arkadiraf/Trixel-LED/Bootloader/SparkFun ISP Pogo Adapter - KIT-11591 - SparkFun Electronics_files/09173-02-L.jpg

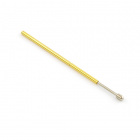
Bootloader/SparkFun ISP Pogo Adapter - KIT-11591 - SparkFun Electronics_files/09173-02-L.jpg
