arkadiraf/Trixel-LED/Bootloader/SparkFun ISP Pogo Adapter - KIT-11591 - SparkFun Electronics_files/09174-02-L.jpg

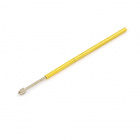
Bootloader/SparkFun ISP Pogo Adapter - KIT-11591 - SparkFun Electronics_files/09174-02-L.jpg
