arkadiraf/Trixel-LED/Bootloader/SparkFun ISP Pogo Adapter - KIT-11591 - SparkFun Electronics_files/09215-3.jpg

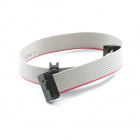
Bootloader/SparkFun ISP Pogo Adapter - KIT-11591 - SparkFun Electronics_files/09215-3.jpg
