arkadiraf/Trixel-LED/Bootloader/SparkFun ISP Pogo Adapter - KIT-11591 - SparkFun Electronics_files/10914-01.jpg

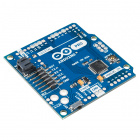
Bootloader/SparkFun ISP Pogo Adapter - KIT-11591 - SparkFun Electronics_files/10914-01.jpg
