arkadiraf/Trixel-LED/Bootloader/SparkFun ISP Pogo Adapter - KIT-11591 - SparkFun Electronics_files/14747-SparkFun_Pi_AVR_Programmer_HAT_-07.jpg

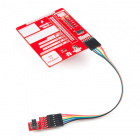
Bootloader/SparkFun ISP Pogo Adapter - KIT-11591 - SparkFun Electronics_files/14747-SparkFun_Pi_AVR_Programmer_HAT_-07.jpg
