arkadiraf/Trixel-LED/Bootloader/USBASP V2.0 Programmer for Atmel Microcontrollers - Art of Circuits_files/60x-9595-microscope-1-150x150.png

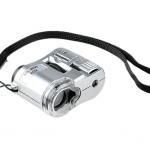
Bootloader/USBASP V2.0 Programmer for Atmel Microcontrollers - Art of Circuits_files/60x-9595-microscope-1-150x150.png
