arkadiraf/Trixel-LED/Bootloader/USBASP V2.0 Programmer for Atmel Microcontrollers - Art of Circuits_files/AVR-ISP-Adapter-10p-6p-1-150x150.jpg

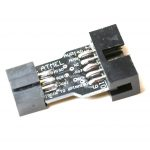
Bootloader/USBASP V2.0 Programmer for Atmel Microcontrollers - Art of Circuits_files/AVR-ISP-Adapter-10p-6p-1-150x150.jpg
