arkadiraf/Trixel-LED/Bootloader/USBASP V2.0 Programmer for Atmel Microcontrollers - Art of Circuits_files/DP30V5A-L_Digital_Power_Supply-1-150x150.jpg

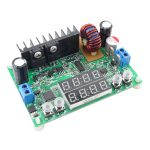
Bootloader/USBASP V2.0 Programmer for Atmel Microcontrollers - Art of Circuits_files/DP30V5A-L_Digital_Power_Supply-1-150x150.jpg
