arkadiraf/Trixel-LED/Bootloader/USBASP V2.0 Programmer for Atmel Microcontrollers - Art of Circuits_files/ELM327-OBD-Bluetooth-Tool-1-150x150.jpg

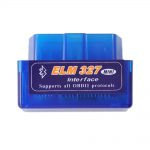
Bootloader/USBASP V2.0 Programmer for Atmel Microcontrollers - Art of Circuits_files/ELM327-OBD-Bluetooth-Tool-1-150x150.jpg
