arkadiraf/Trixel-LED/Bootloader/USBASP V2.0 Programmer for Atmel Microcontrollers - Art of Circuits_files/NodeMCU-LUA-R2-1-150x150.png

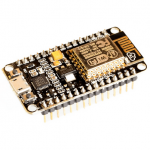
Bootloader/USBASP V2.0 Programmer for Atmel Microcontrollers - Art of Circuits_files/NodeMCU-LUA-R2-1-150x150.png
