arkadiraf/Trixel-LED/Bootloader/USBASP V2.0 Programmer for Atmel Microcontrollers - Art of Circuits_files/Ultrasonic-Distance-Meter-CP3007-150x150.jpg

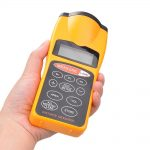
Bootloader/USBASP V2.0 Programmer for Atmel Microcontrollers - Art of Circuits_files/Ultrasonic-Distance-Meter-CP3007-150x150.jpg
