arkadiraf/Trixel-LED/Bootloader/USBASP V2.0 Programmer for Atmel Microcontrollers - Art of Circuits_files/Xilinx-Platform-USB-Cable-DLC9LP-1a-150x150.jpg

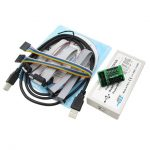
Bootloader/USBASP V2.0 Programmer for Atmel Microcontrollers - Art of Circuits_files/Xilinx-Platform-USB-Cable-DLC9LP-1a-150x150.jpg
