arkadiraf/Trixel-LED/Eagle/Single Side/Paneling/MiniPanel V01/design versions - temp/FullPanel.JPG

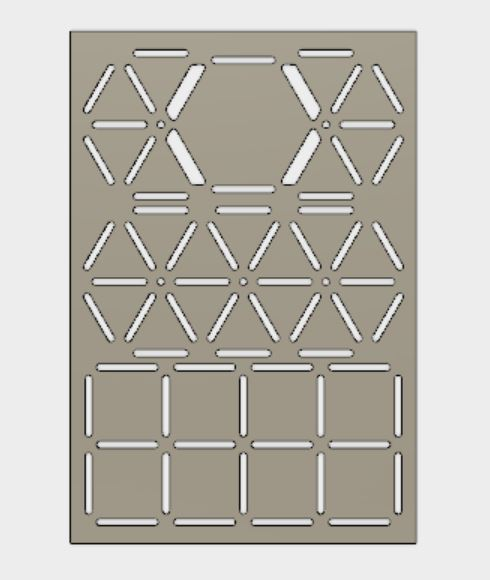
Eagle/Single Side/Paneling/MiniPanel V01/design versions - temp/FullPanel.JPG
