arkadiraf/Trixel-LED/Eagle/Single Side/Paneling/MiniPanel V01/design versions - temp/MiniPanel V01 Bot.png

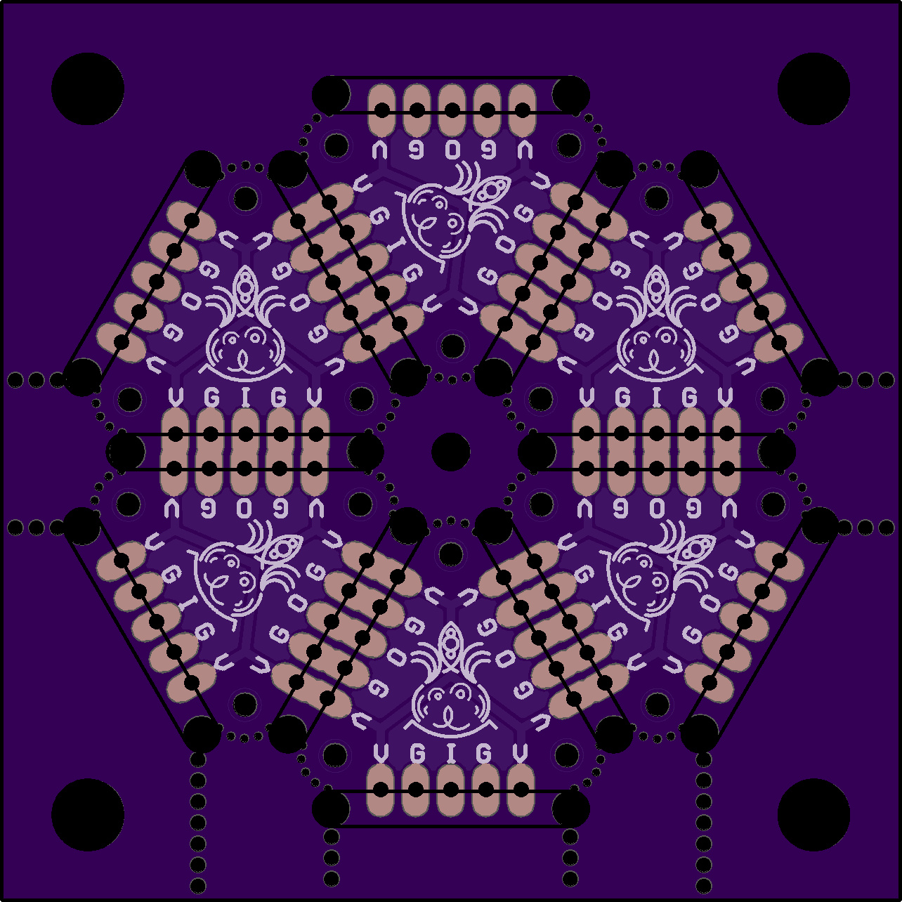
Eagle/Single Side/Paneling/MiniPanel V01/design versions - temp/MiniPanel V01 Bot.png
