arkadiraf/Trixel-LED/Eagle/Single Side/Paneling/MiniPanel V01/design versions - temp/Top_Panel.png

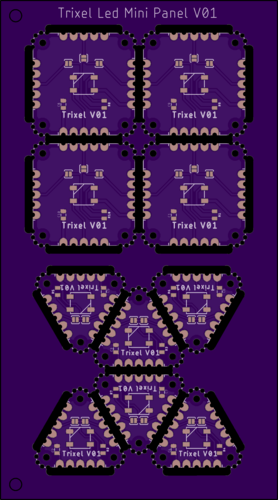
Eagle/Single Side/Paneling/MiniPanel V01/design versions - temp/Top_Panel.png
