arkadiraf/Trixel-LED/Eagle/Single Side/Paneling/MiniPanel V01/design versions - temp/TrixelLedShape.jpg

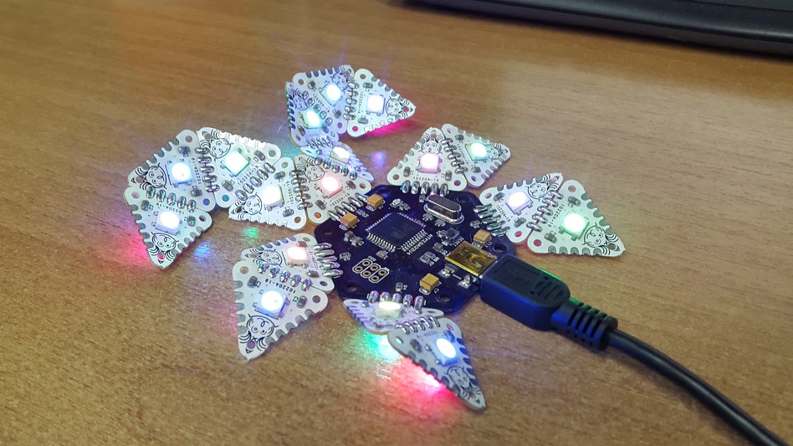
Eagle/Single Side/Paneling/MiniPanel V01/design versions - temp/TrixelLedShape.jpg
