arkadiraf/Trixel-LED/Images/20161030_152325.jpg

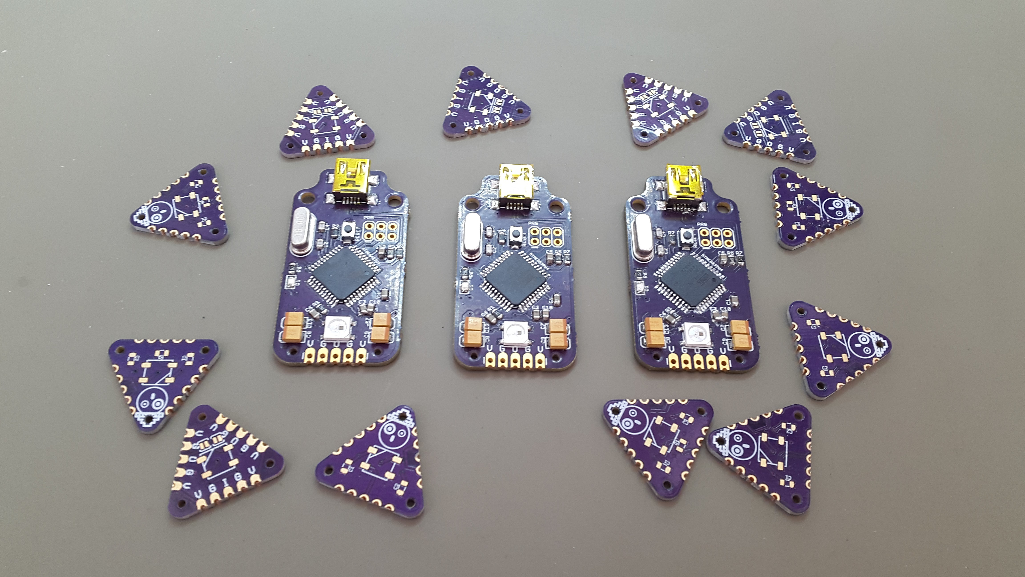
Images/20161030_152325.jpg
