arkadiraf/Trixel-LED/Images/20161031_134225.jpg

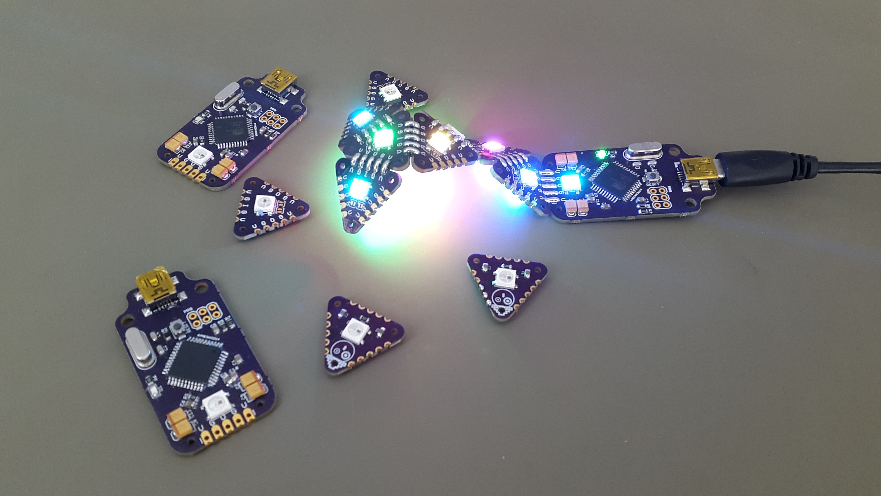
Images/20161031_134225.jpg
