arkadiraf/Trixel-LED/Images/20161031_134325.jpg

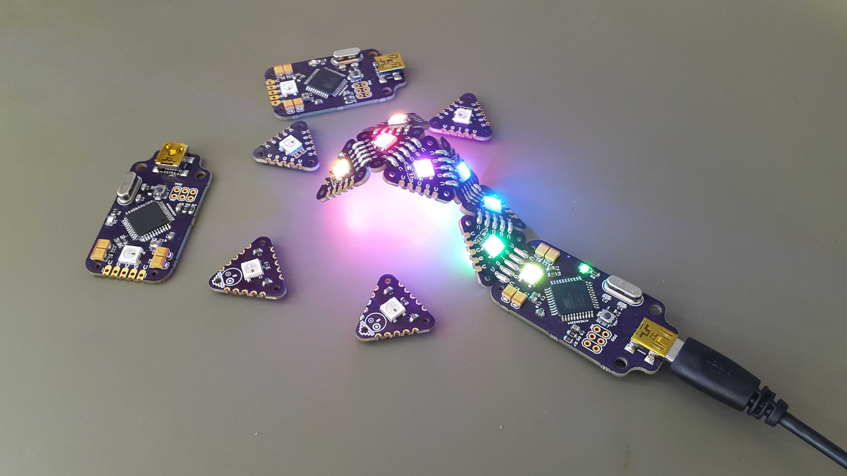
Images/20161031_134325.jpg
