arkadiraf/Trixel-LED/Images/20161214_113320.jpg

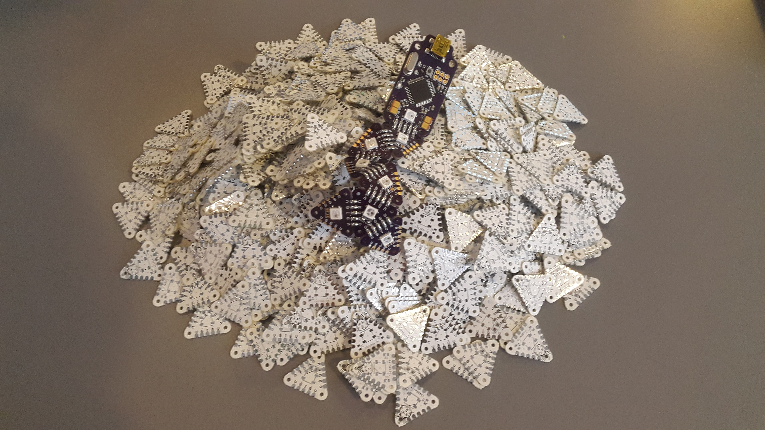
Images/20161214_113320.jpg
