arkadiraf/Trixel-LED/Images/20170321_155306.jpg

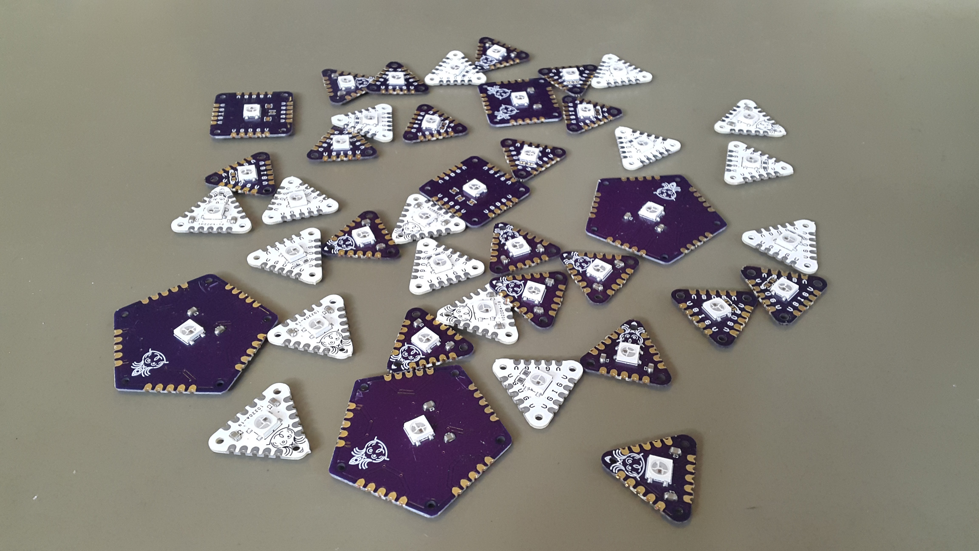
Images/20170321_155306.jpg
