arkadiraf/Trixel-LED/Images/20170321_155313.jpg

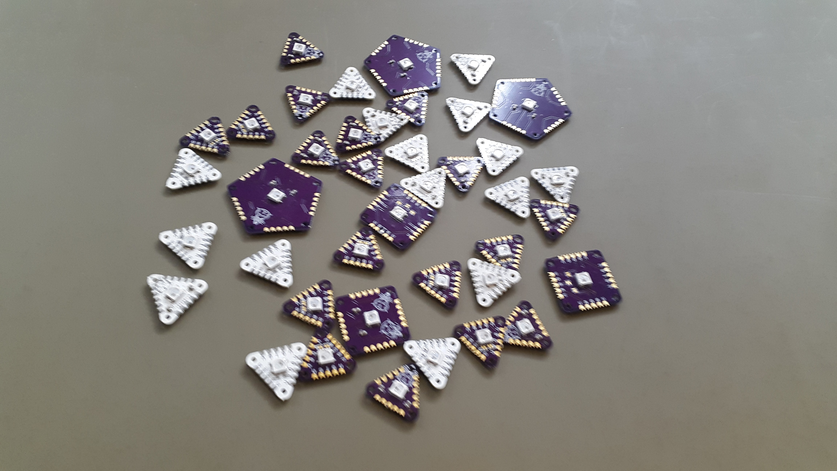
Images/20170321_155313.jpg
