arkadiraf/Trixel-LED/Images/20170321_155402.jpg

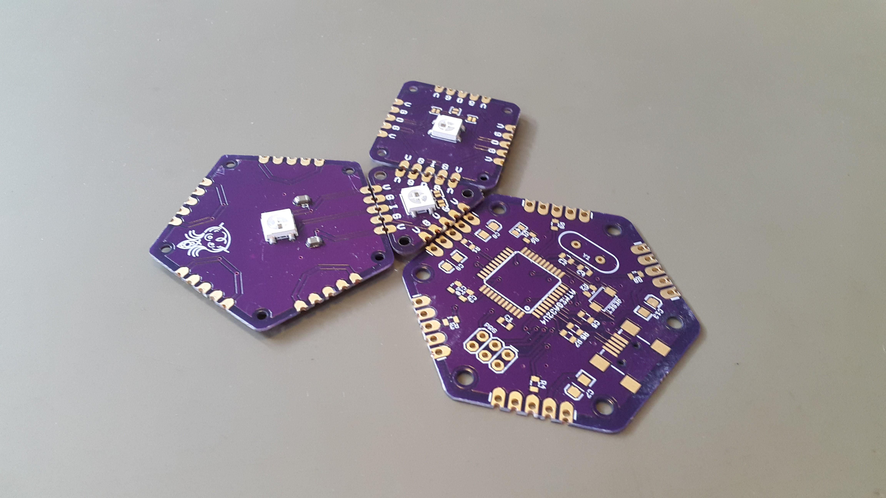
Images/20170321_155402.jpg
