arkadiraf/Trixel-LED/Images/20170321_155528.jpg

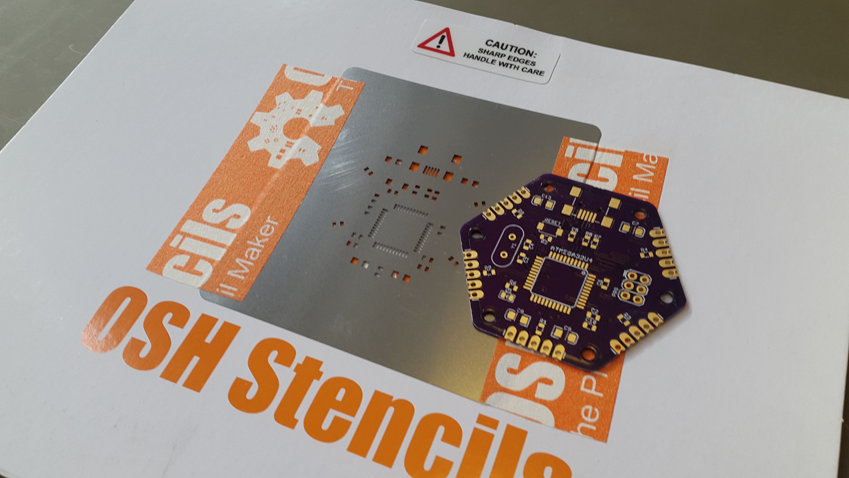
Images/20170321_155528.jpg
