arkadiraf/Trixel-LED/Images/20170321_155751.jpg

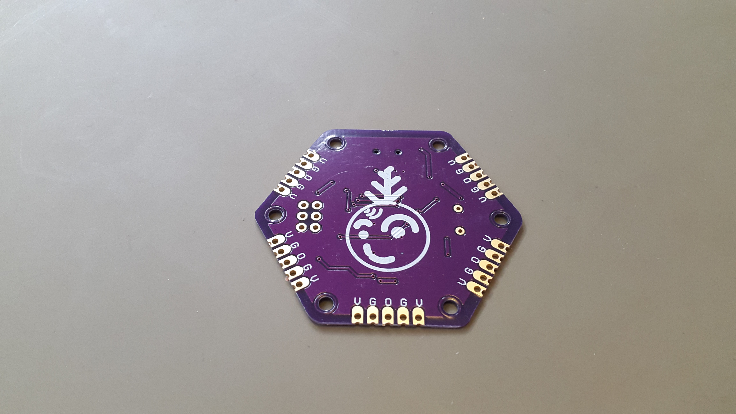
Images/20170321_155751.jpg
