arkadiraf/Trixel-LED/Images/20180521_083153.jpg

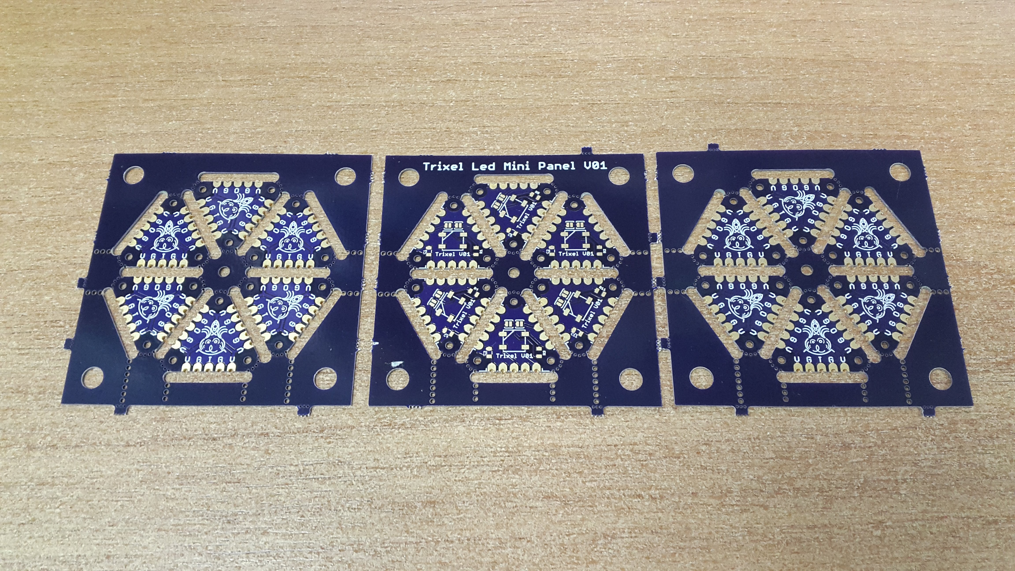
Images/20180521_083153.jpg
