arkadiraf/Trixel-LED/Images/20180521_110222-ANIMATION.gif

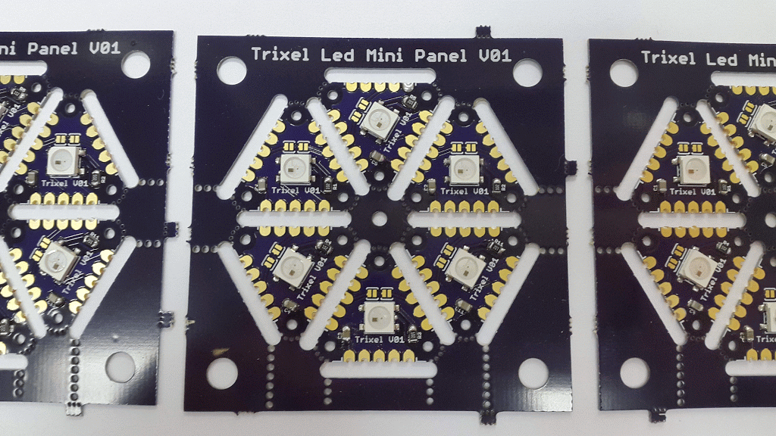
Images/20180521_110222-ANIMATION.gif
