arkadiraf/Trixel-LED/Images/20180521_110649.jpg

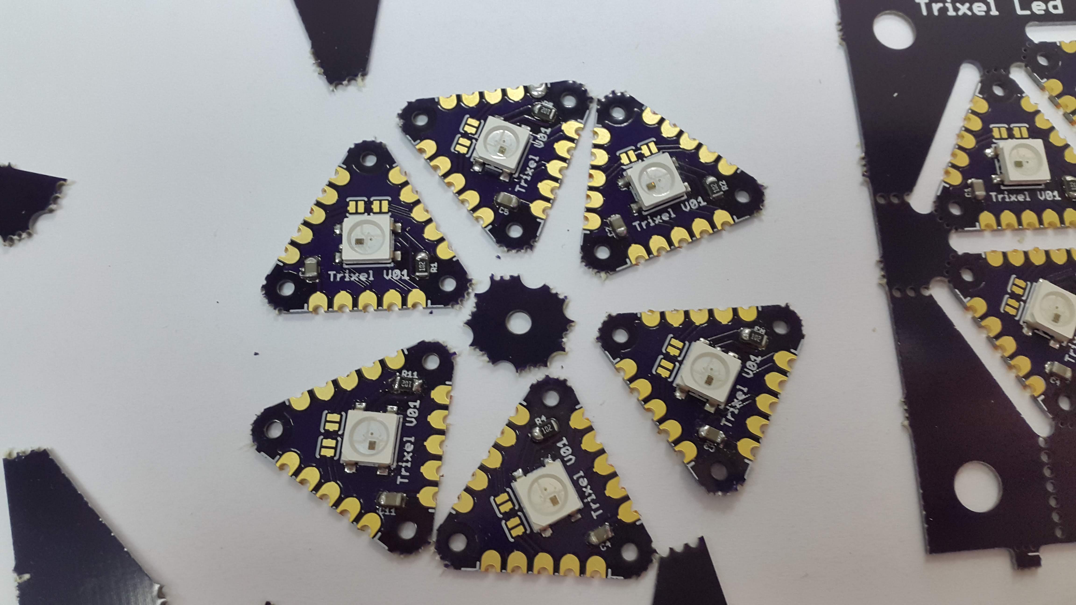
Images/20180521_110649.jpg
