arkadiraf/Trixel-LED/Images/20180524_122904.jpg

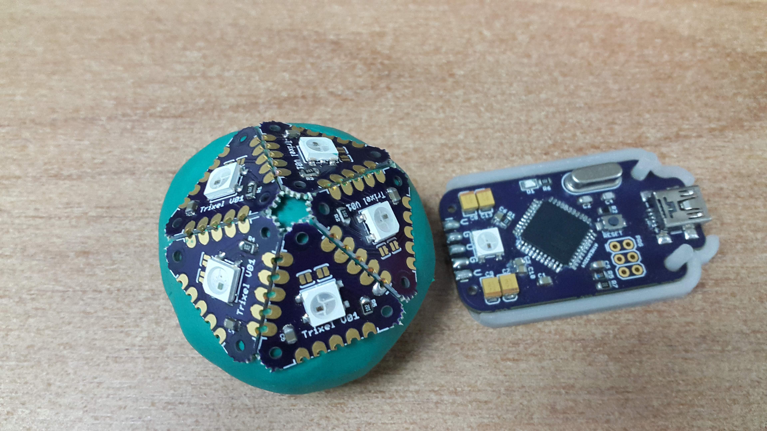
Images/20180524_122904.jpg
