arkadiraf/Trixel-LED/Images/20180524_124214.jpg

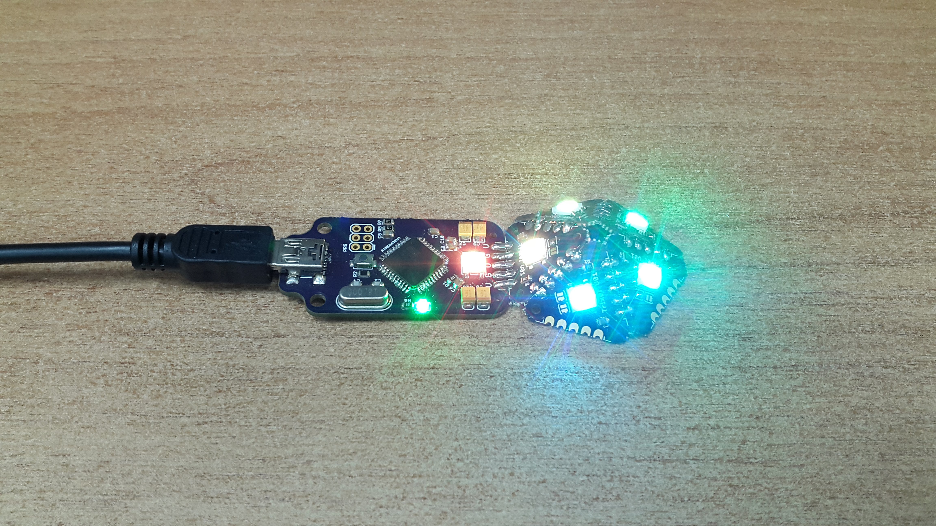
Images/20180524_124214.jpg
