arkadiraf/Trixel-LED/Images/20200722_104454.jpg

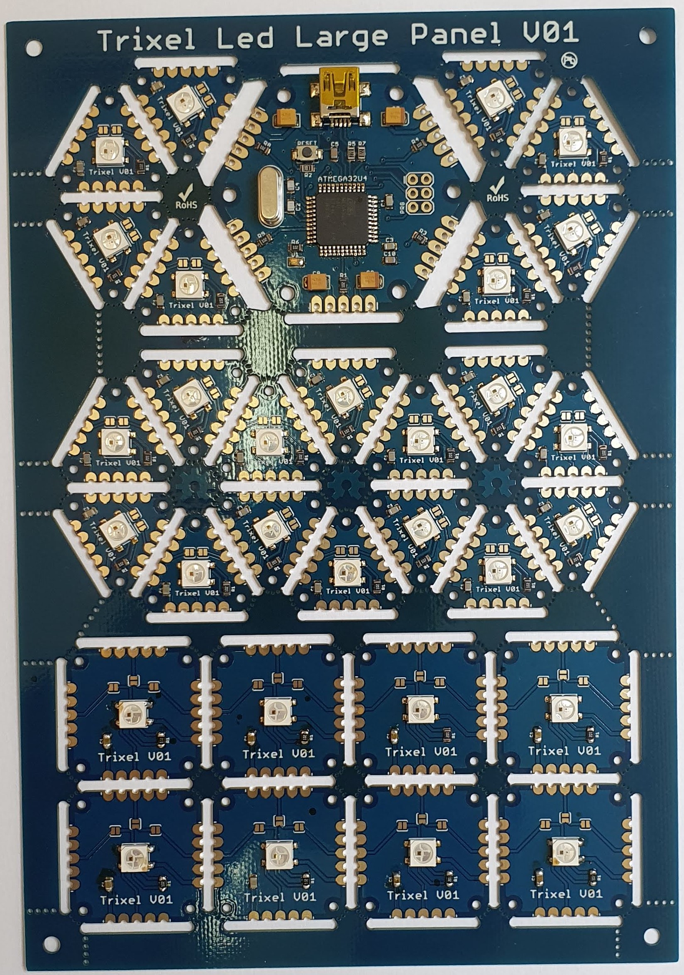
Images/20200722_104454.jpg
