arkadiraf/Trixel-LED/Images/20200722_104515.jpg

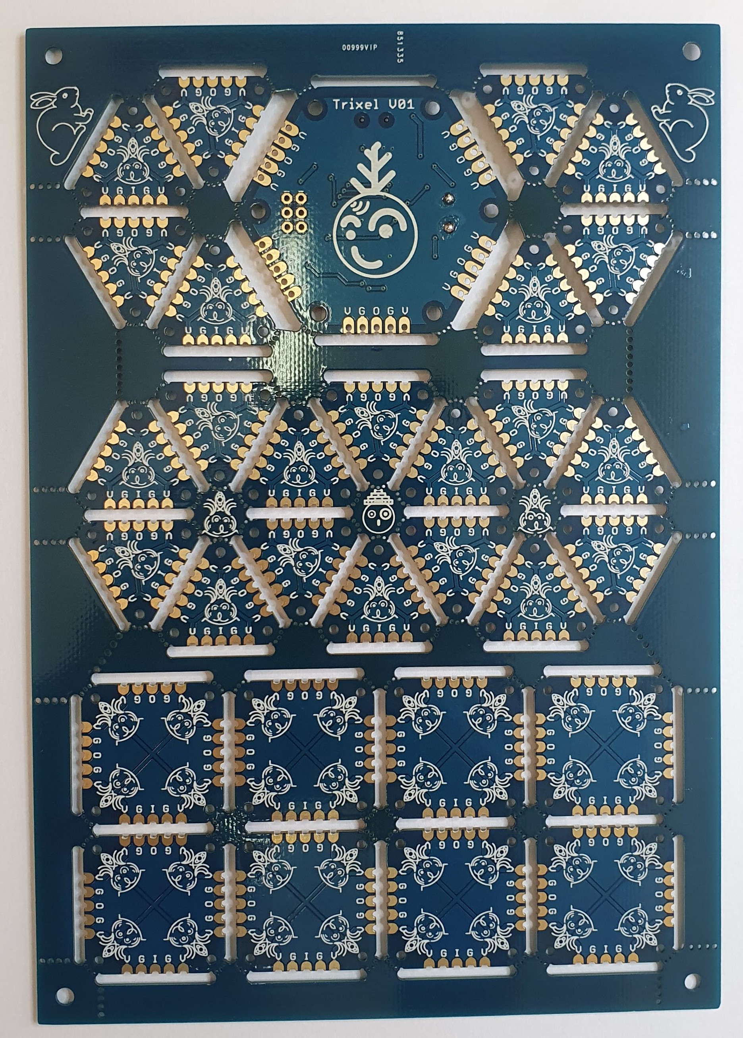
Images/20200722_104515.jpg
