arkadiraf/Trixel-LED/Images/20200722_111059.jpg

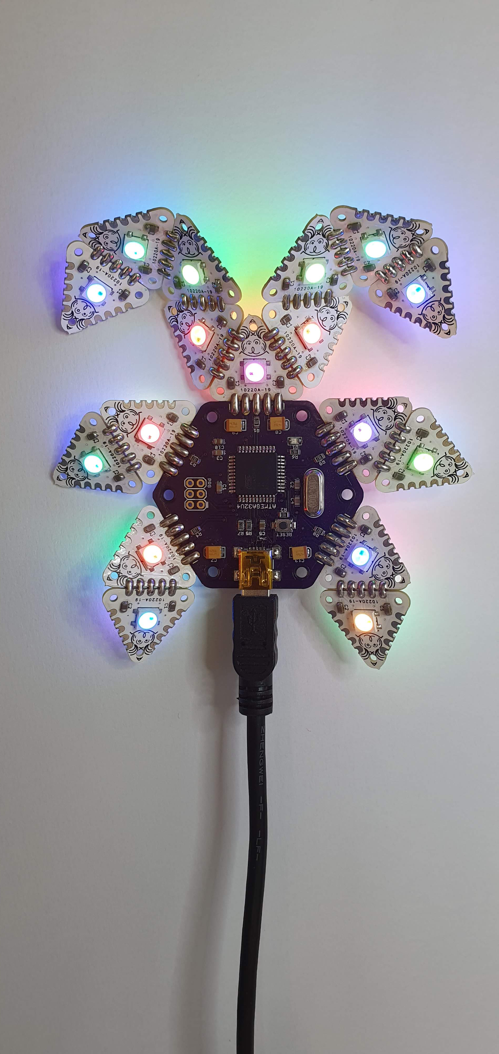
Images/20200722_111059.jpg
