arkadiraf/Trixel-LED/Images/20200722_111215.jpg

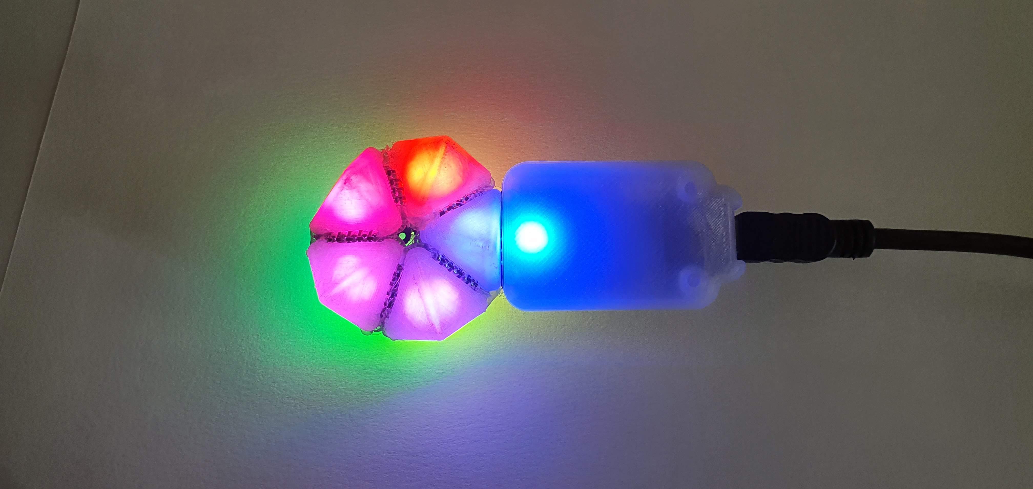
Images/20200722_111215.jpg
