arkadiraf/Trixel-LED/Images/IMG_1216.jpg

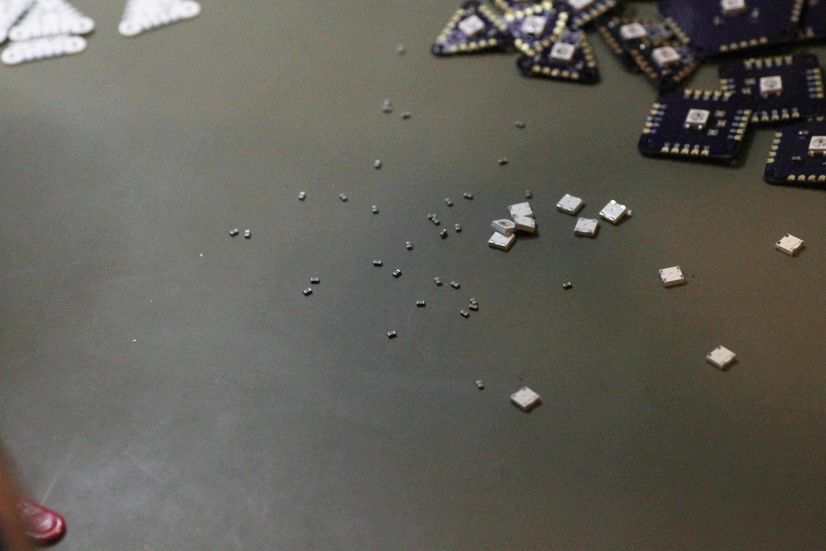
Images/IMG_1216.jpg
