arkadiraf/Trixel-LED/Bootloader/SparkFun ISP Pogo Adapter - KIT-11591 - SparkFun Electronics_files/14640-heART_-_Surface_Mount_Soldering_Kit-01.jpg

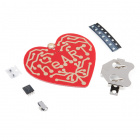
Bootloader/SparkFun ISP Pogo Adapter - KIT-11591 - SparkFun Electronics_files/14640-heART_-_Surface_Mount_Soldering_Kit-01.jpg
