arkadiraf/Trixel-LED/Bootloader/SparkFun ISP Pogo Adapter - KIT-11591 - SparkFun Electronics_files/15797-MPLAB_PICkit_4_In-Circuit_Debugger-01.jpg

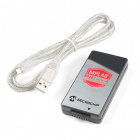
Bootloader/SparkFun ISP Pogo Adapter - KIT-11591 - SparkFun Electronics_files/15797-MPLAB_PICkit_4_In-Circuit_Debugger-01.jpg
